noahknorr/mri-climate-chamber/3d-files/STLs/schlauchverbinderSchnellverschluss_verbinderHochflexibel-PVC_6.stl

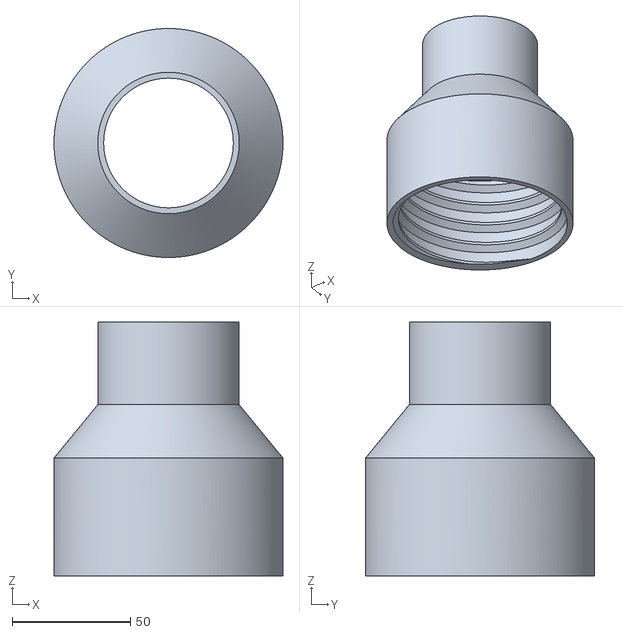
[picture p15: CAD file, 2026-01-19]
3d-files/STLs/schlauchverbinderSchnellverschluss_verbinderHochflexibel-PVC_6.stl
97.0 x 97.0 x 107.6
