noahknorr/mri-climate-chamber/3d-files/STLs/einsatz_SILKSCREEN_BOTTOM_36.stl

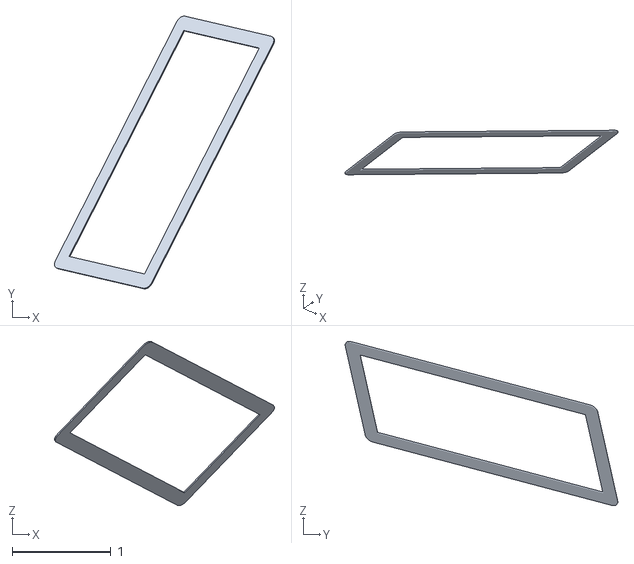
[picture p16: CAD file, 2026-01-19]
3d-files/STLs/einsatz_SILKSCREEN_BOTTOM_36.stl
2.23 x 2.77 x 1.67
