noahknorr/mri-climate-chamber/3d-files/STLs/schlauchverbinderSchnellverschluss_anschlussSuperflex_4.stl

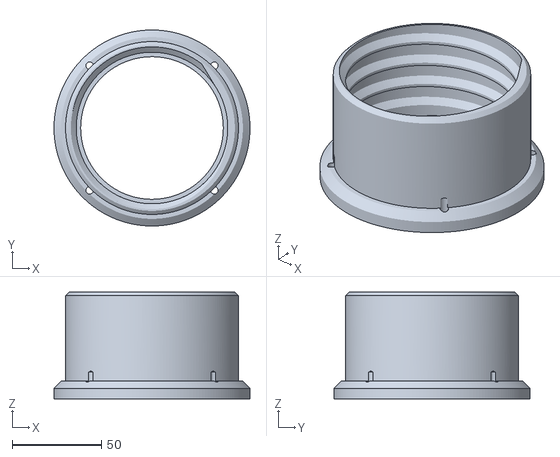
[picture p17: CAD file, 2026-01-19]
3d-files/STLs/schlauchverbinderSchnellverschluss_anschlussSuperflex_4.stl
110.0 x 110.0 x 60.0
