noahknorr/mri-climate-chamber/3d-files/STLs/einsatz_Dielectric_32.stl

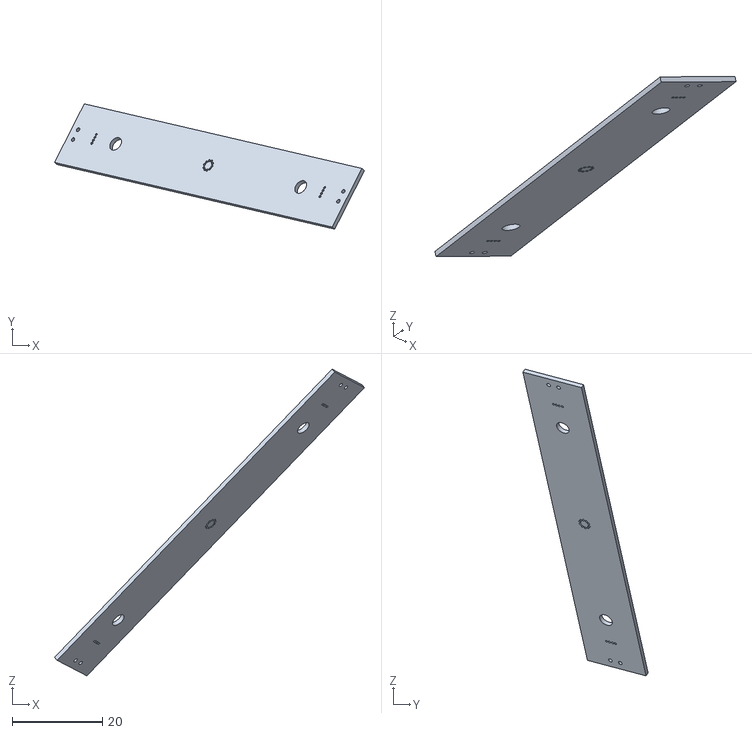
[picture p18: CAD file, 2026-01-19]
3d-files/STLs/einsatz_Dielectric_32.stl
68.8 x 27.8 x 68.1
