noahknorr/mri-climate-chamber/3d-files/STLs/einsatz_K1_18.stl

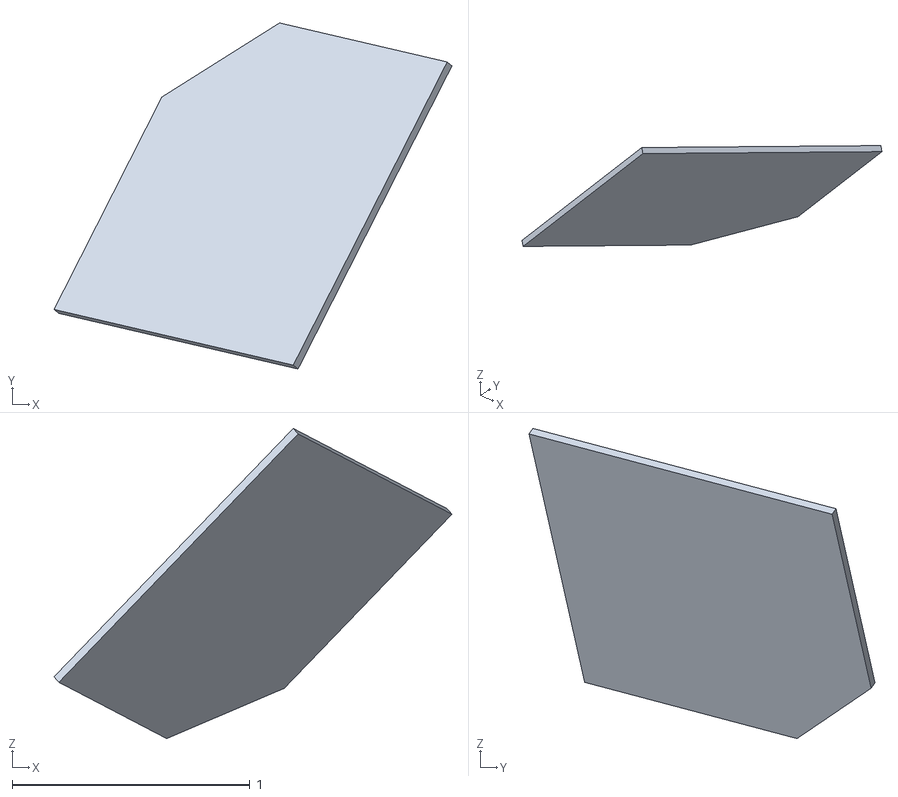
[picture p19: CAD file, 2026-01-19]
3d-files/STLs/einsatz_K1_18.stl
1.67 x 1.46 x 1.31
