noahknorr/mri-climate-chamber/3d-files/STLs/einsatz_bogenVerbinder_48.stl

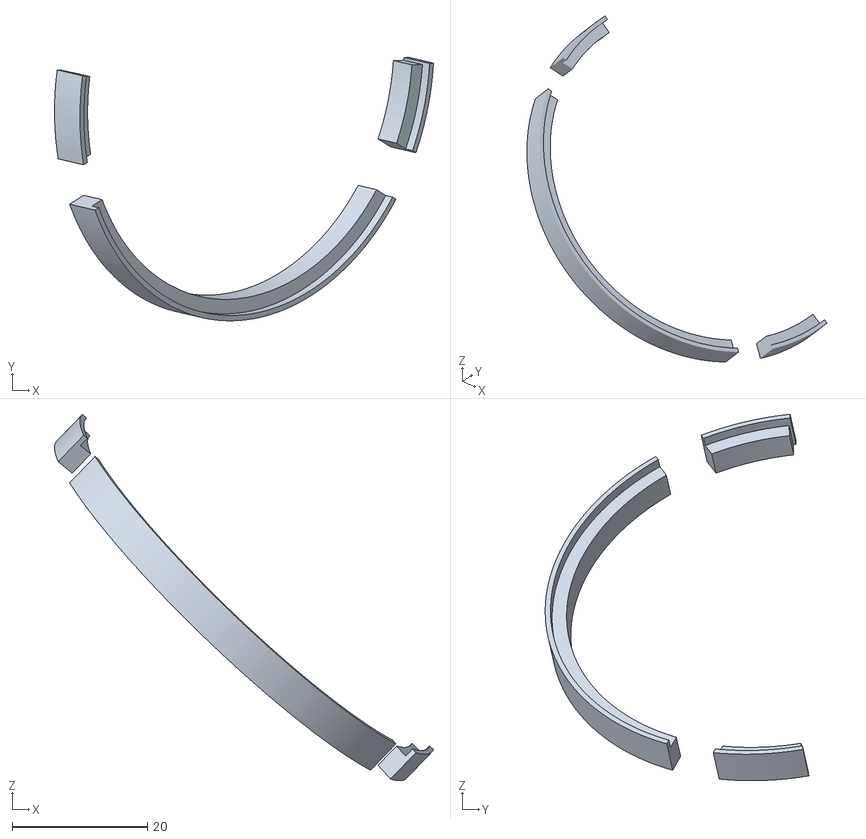
[picture p20: CAD file, 2026-01-19]
3d-files/STLs/einsatz_bogenVerbinder_48.stl
56.1 x 39.0 x 54.2
