noahknorr/mri-climate-chamber/3d-files/STLs/einsatz_HL2X_37.stl

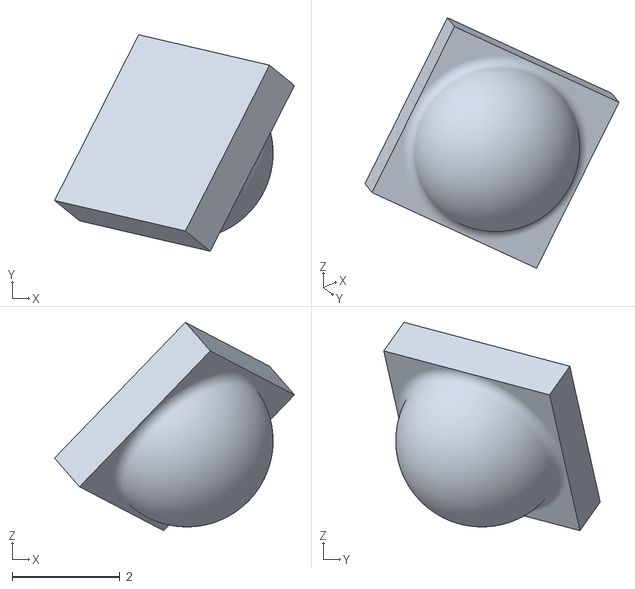
[picture p21: CAD file, 2026-01-19]
3d-files/STLs/einsatz_HL2X_37.stl
4.46 x 4.02 x 3.87
