noahknorr/mri-climate-chamber/3d-files/STLs/einsatz_TOP_31.stl

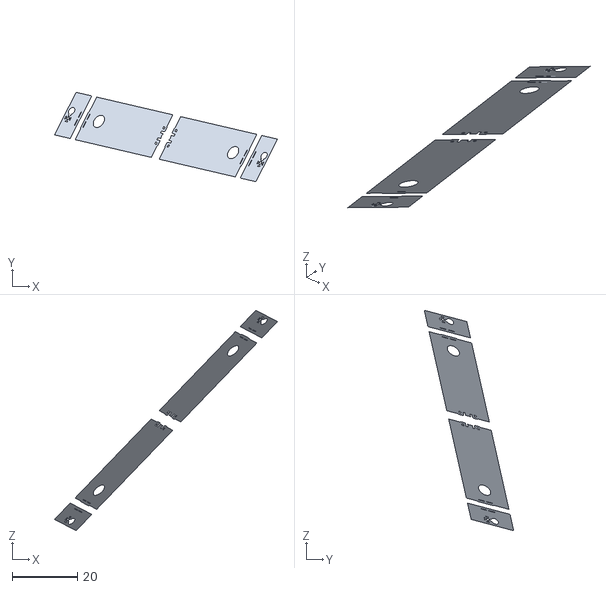
[picture p22: CAD file, 2026-01-19]
3d-files/STLs/einsatz_TOP_31.stl
68.3 x 27.4 x 67.5
