noahknorr/mri-climate-chamber/3d-files/STLs/einsatz_PIN_4_26.stl

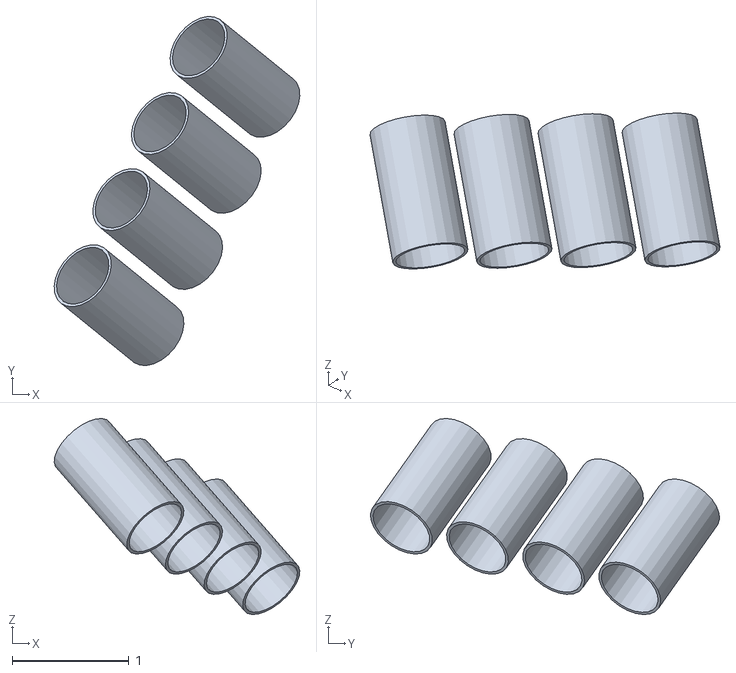
[picture p23: CAD file, 2026-01-19]
3d-files/STLs/einsatz_PIN_4_26.stl
2.10 x 2.98 x 1.68
