noahknorr/mri-climate-chamber/3d-files/STLs/einsatz_PASTEMASK_BOTTOM_35.stl

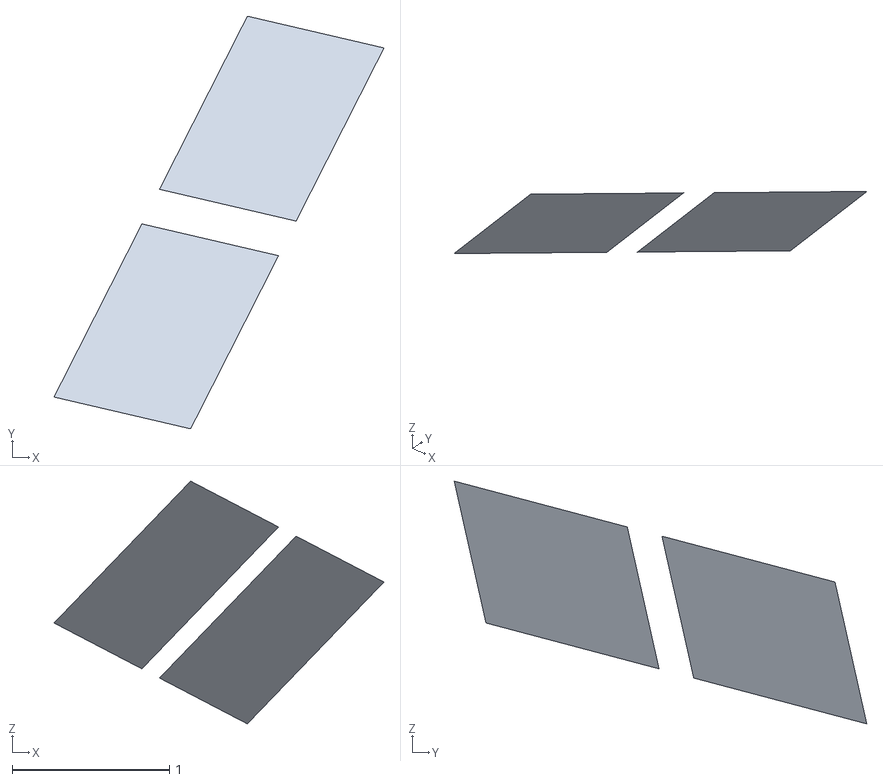
[picture p24: CAD file, 2026-01-19]
3d-files/STLs/einsatz_PASTEMASK_BOTTOM_35.stl
2.10 x 2.63 x 1.55
