noahknorr/mri-climate-chamber/3d-files/STLs/einsatz_1_2_4.stl

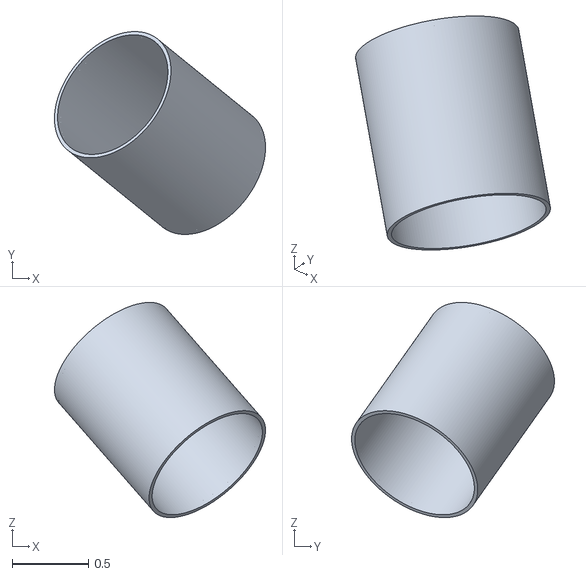
[picture p25: CAD file, 2026-01-19]
3d-files/STLs/einsatz_1_2_4.stl
1.39 x 1.33 x 1.41
