noahknorr/mri-climate-chamber/3d-files/STLs/einsatz_2_3_10.stl

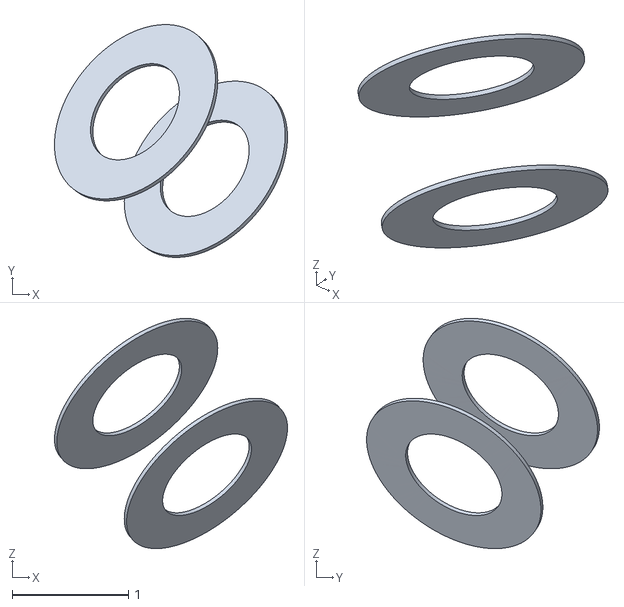
[picture p26: CAD file, 2026-01-19]
3d-files/STLs/einsatz_2_3_10.stl
2.01 x 2.01 x 1.98
