noahknorr/mri-climate-chamber/3d-files/STLs/einsatz_PFOSTEN_2P_41.stl

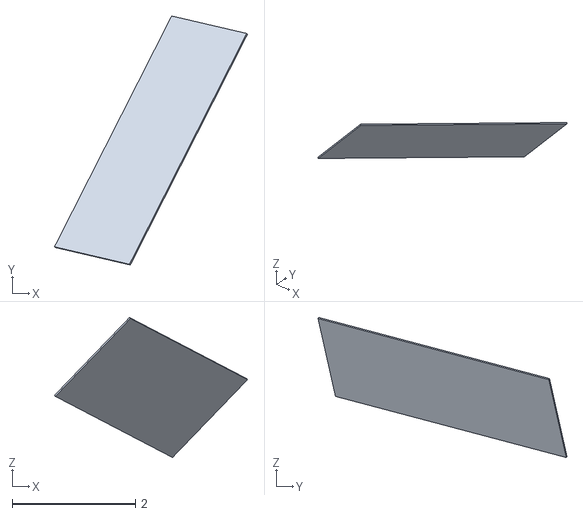
[picture p27: CAD file, 2026-01-19]
3d-files/STLs/einsatz_PFOSTEN_2P_41.stl
3.13 x 4.04 x 2.27
