noahknorr/mri-climate-chamber/3d-files/STLs/schlauchverbinderSchnellverschluss_grundeinsatz_1.stl

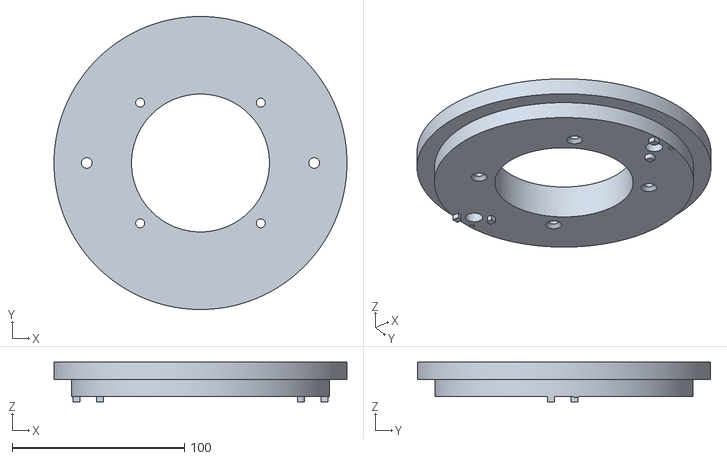
[picture p28: CAD file, 2026-01-19]
3d-files/STLs/schlauchverbinderSchnellverschluss_grundeinsatz_1.stl
170.0 x 170.0 x 23.0
