noahknorr/mri-climate-chamber/3d-files/STLs/schlauchverbinderSchnellverschluss_riegel_3.stl

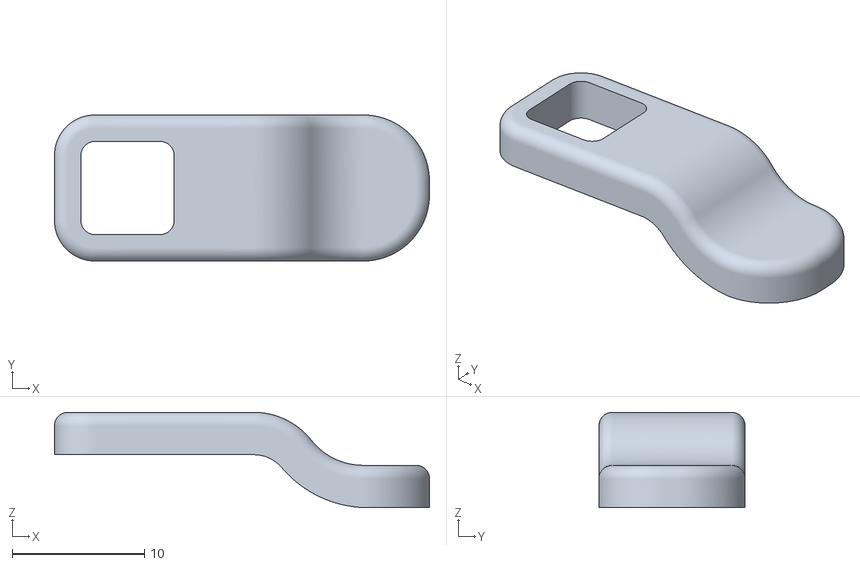
[picture p29: CAD file, 2026-01-19]
3d-files/STLs/schlauchverbinderSchnellverschluss_riegel_3.stl
28.3 x 11.0 x 7.20
