noahknorr/mri-climate-chamber/3d-files/STLs/schlauchverbinderSchnellverschluss_verbinderHebelRiegel_2.stl

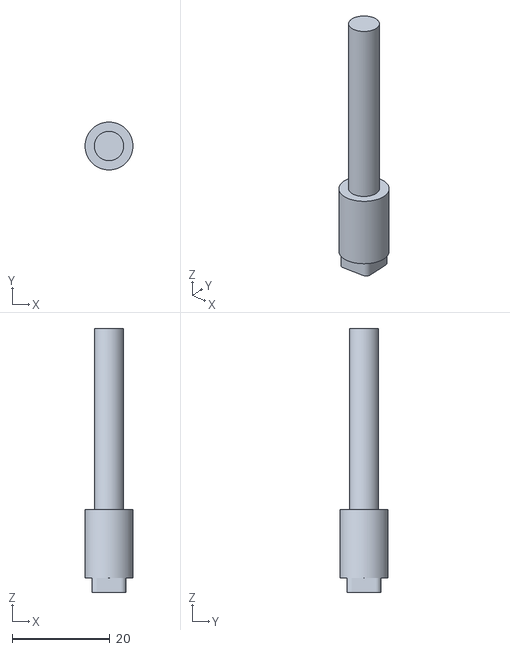
[picture p30: CAD file, 2026-01-19]
3d-files/STLs/schlauchverbinderSchnellverschluss_verbinderHebelRiegel_2.stl
9.80 x 9.79 x 54.0
