noahknorr/mri-climate-chamber/3d-files/STLs/einsatz_verbinderGrundrohrLaschen_47.stl

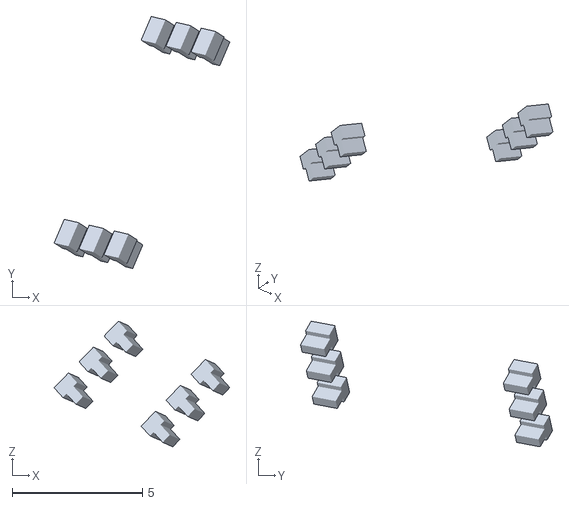
[picture p31: CAD file, 2026-01-19]
3d-files/STLs/einsatz_verbinderGrundrohrLaschen_47.stl
6.75 x 9.68 x 4.82
