noahknorr/mri-climate-chamber/3d-files/STLs/einsatz_aufsatzManschette_51.stl

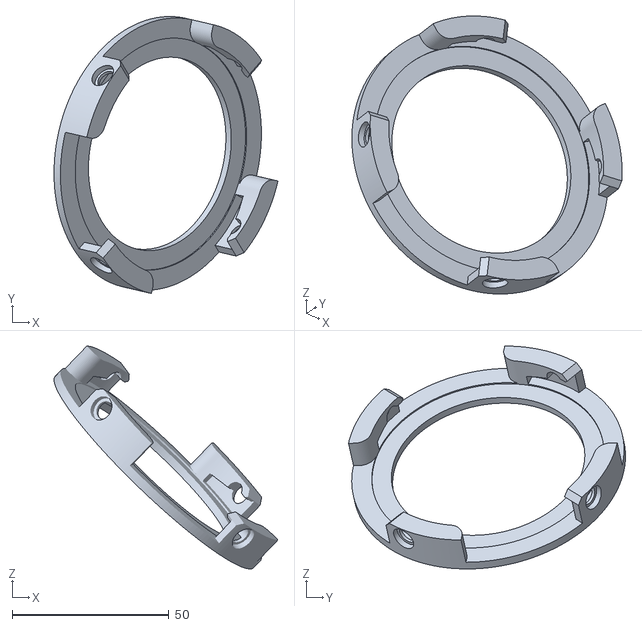
[picture p32: CAD file, 2026-01-19]
3d-files/STLs/einsatz_aufsatzManschette_51.stl
71.5 x 88.4 x 71.1
