noahknorr/mri-climate-chamber/3d-files/STLs/einsatz_verbinderPVC-Bajonett_54.stl

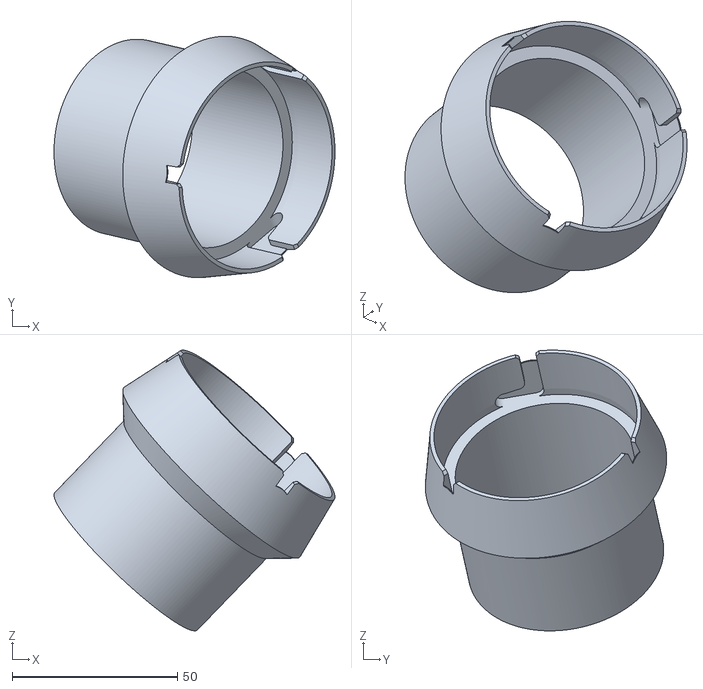
[picture p33: CAD file, 2026-01-19]
3d-files/STLs/einsatz_verbinderPVC-Bajonett_54.stl
85.0 x 73.0 x 84.9
