noahknorr/mri-climate-chamber/3d-files/STLs/einsatz_1_3_5.stl

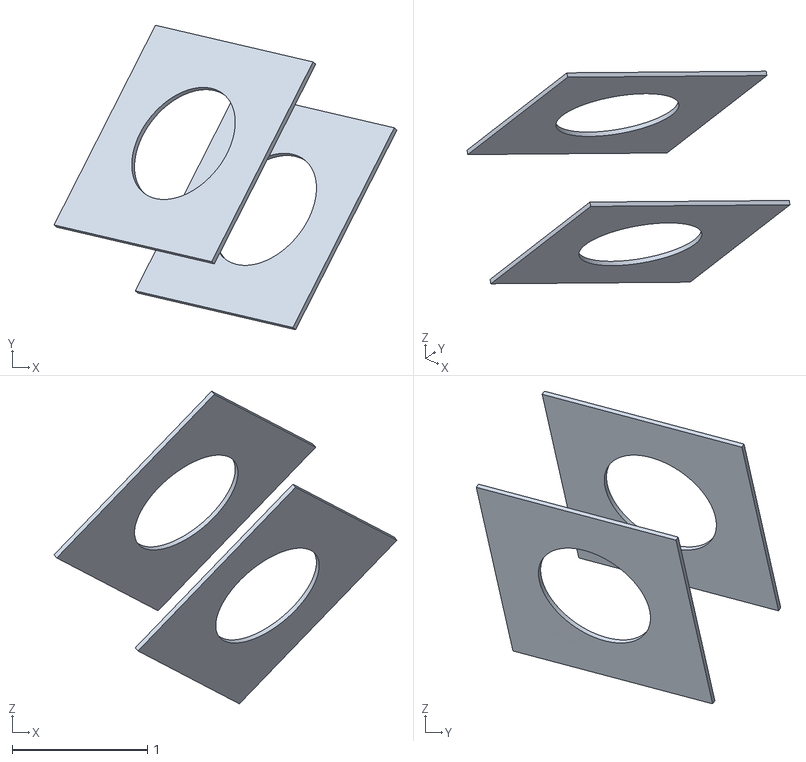
[picture p34: CAD file, 2026-01-19]
3d-files/STLs/einsatz_1_3_5.stl
2.54 x 2.25 x 2.31
