noahknorr/mri-climate-chamber/3d-files/STLs/einsatz_PIN_3_25.stl

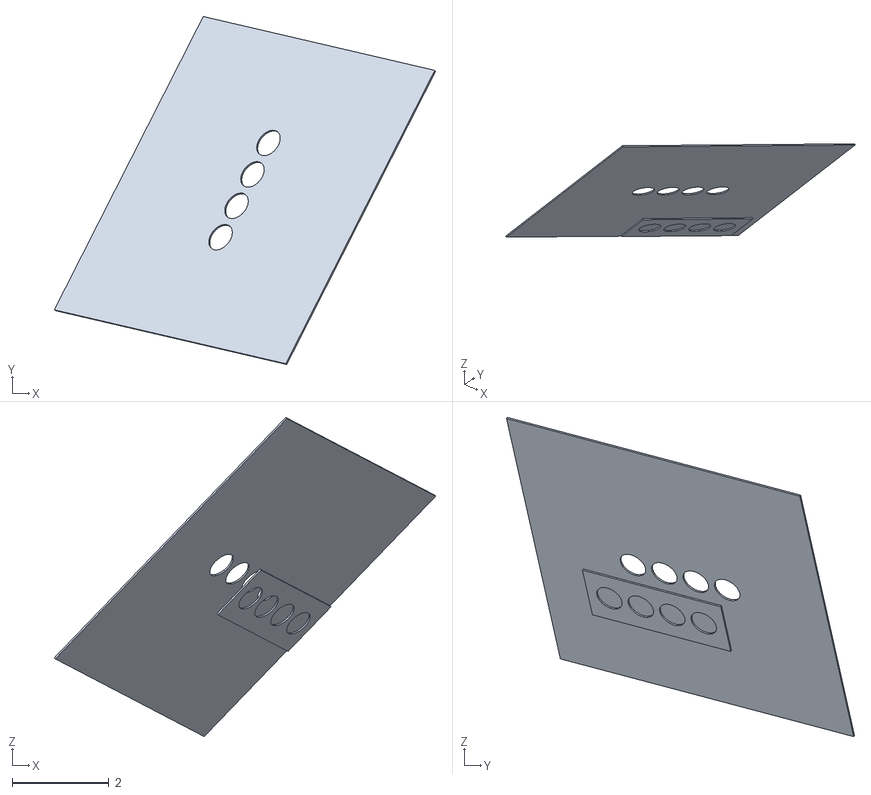
[picture p35: CAD file, 2026-01-19]
3d-files/STLs/einsatz_PIN_3_25.stl
7.90 x 7.21 x 6.61
