noahknorr/mri-climate-chamber/3d-files/STLs/einsatz_verbinderDeckelSeilichGummi2_59.stl

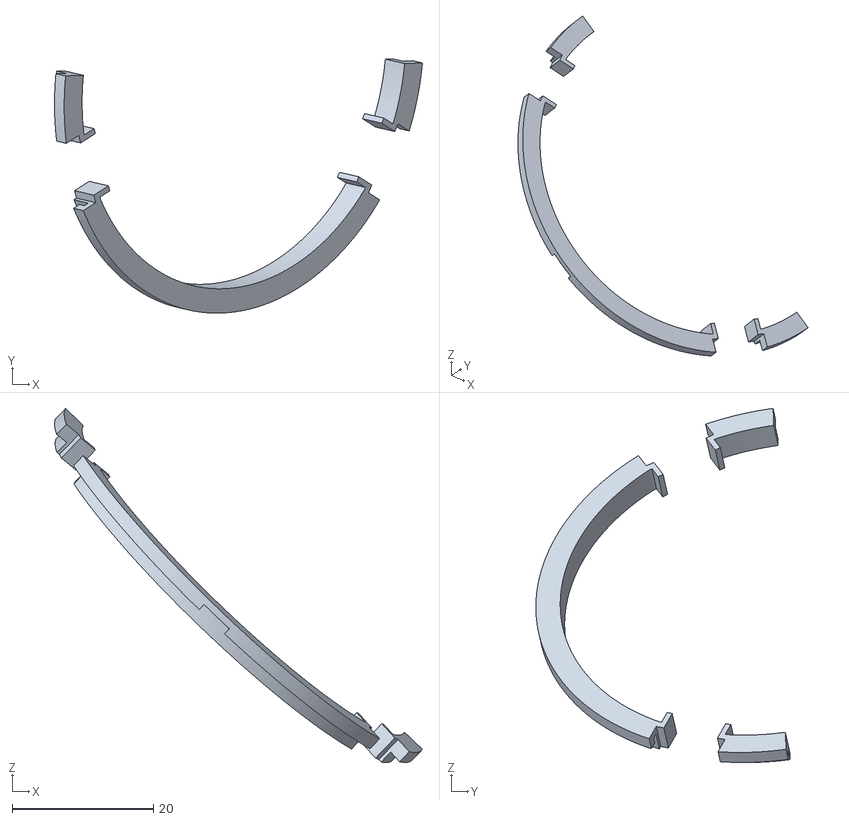
[picture p36: CAD file, 2026-01-19]
3d-files/STLs/einsatz_verbinderDeckelSeilichGummi2_59.stl
52.2 x 36.1 x 50.2
