noahknorr/mri-climate-chamber/3d-files/STLs/einsatz_A1_14.stl

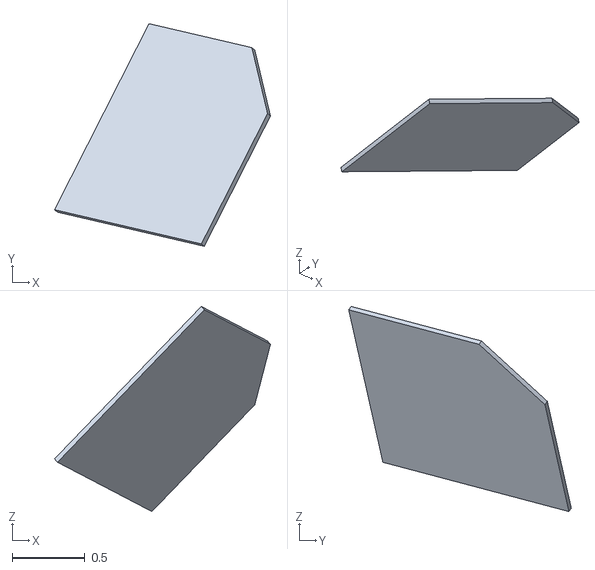
[picture p37: CAD file, 2026-01-19]
3d-files/STLs/einsatz_A1_14.stl
1.48 x 1.53 x 1.41
