noahknorr/mri-climate-chamber/3d-files/STLs/einsatz_SOLDERMASK_TOP_30.stl

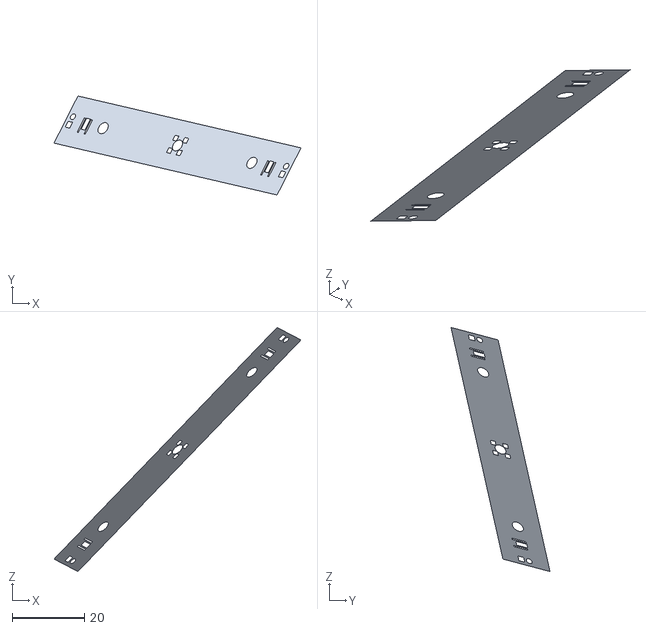
[picture p38: CAD file, 2026-01-19]
3d-files/STLs/einsatz_SOLDERMASK_TOP_30.stl
68.3 x 27.4 x 67.4
