noahknorr/mri-climate-chamber/3d-files/STLs/schlauchverbinderSchnellverschluss_flansch50mmLuefter_5.stl

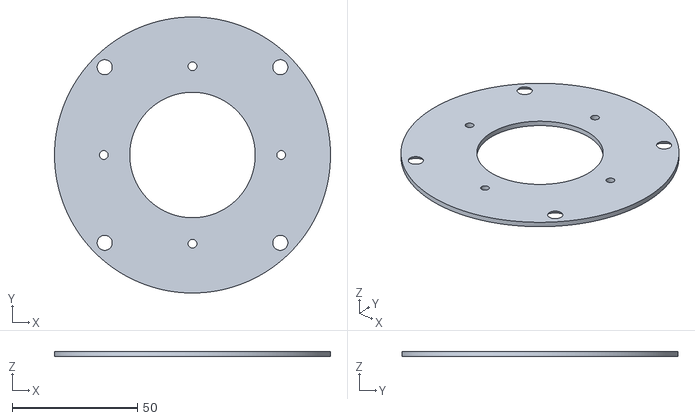
[picture p39: CAD file, 2026-01-19]
3d-files/STLs/schlauchverbinderSchnellverschluss_flansch50mmLuefter_5.stl
110.0 x 110.0 x 2.00
