noahknorr/mri-climate-chamber/3d-files/STLs/einsatz_SILKSCREEN_TOP_28.stl

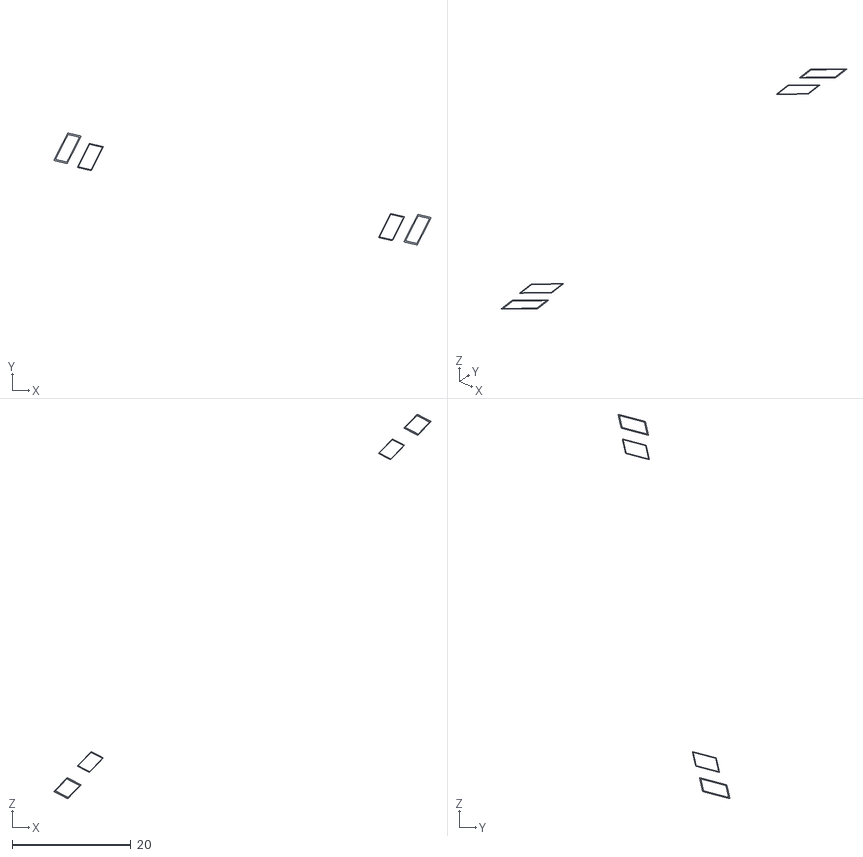
[picture p40: CAD file, 2026-01-19]
3d-files/STLs/einsatz_SILKSCREEN_TOP_28.stl
63.4 x 18.8 x 64.7
