noahknorr/mri-climate-chamber/3d-files/STLs/einsatz_aufsatzStatorStarr_53.stl

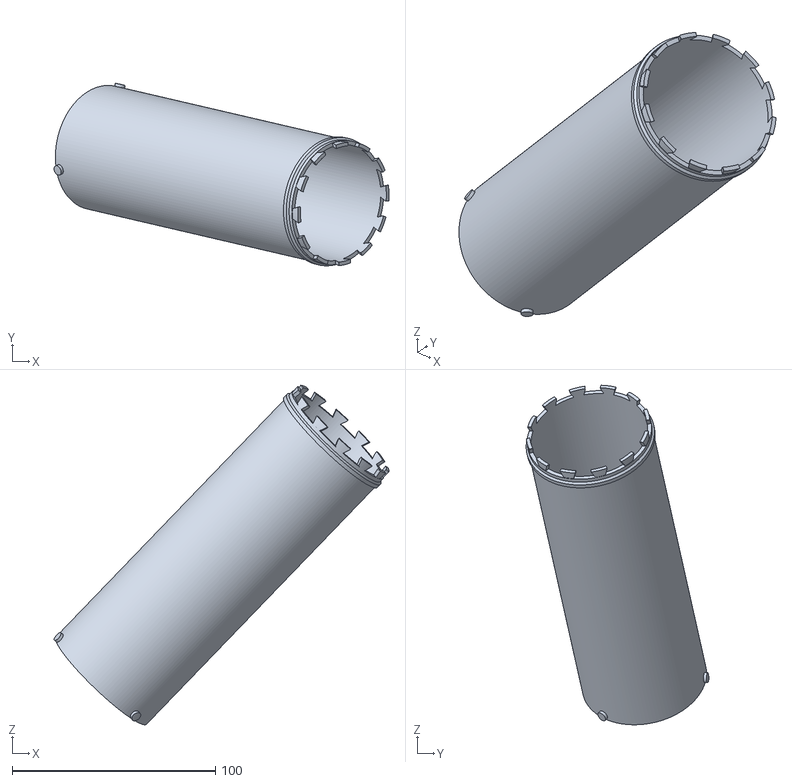
[picture p41: CAD file, 2026-01-19]
3d-files/STLs/einsatz_aufsatzStatorStarr_53.stl
164.9 x 89.9 x 167.1
