noahknorr/mri-climate-chamber/3d-files/STLs/einsatz_PIN_22.stl

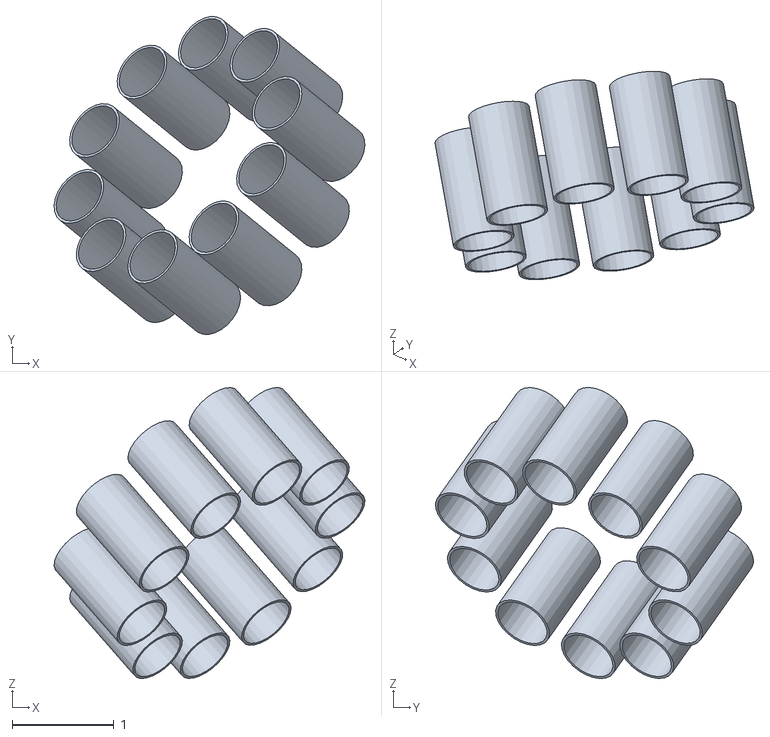
[picture p42: CAD file, 2026-01-19]
3d-files/STLs/einsatz_PIN_22.stl
3.06 x 3.13 x 2.87
