noahknorr/mri-climate-chamber/3d-files/STLs/einsatz_verbinderDeckelSeitlichEinsaetzeMitLaschen_58.stl

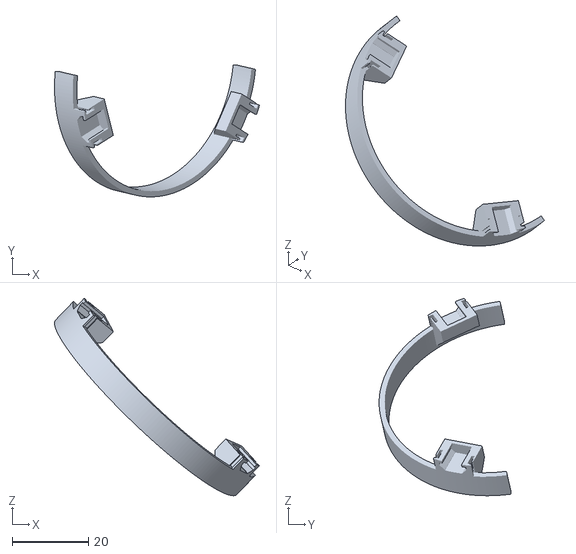
[picture p43: CAD file, 2026-01-19]
3d-files/STLs/einsatz_verbinderDeckelSeitlichEinsaetzeMitLaschen_58.stl
53.7 x 34.6 x 51.8
