noahknorr/mri-climate-chamber/3d-files/STLs/einsatz_LOTBRUCKE_2POL_39.stl

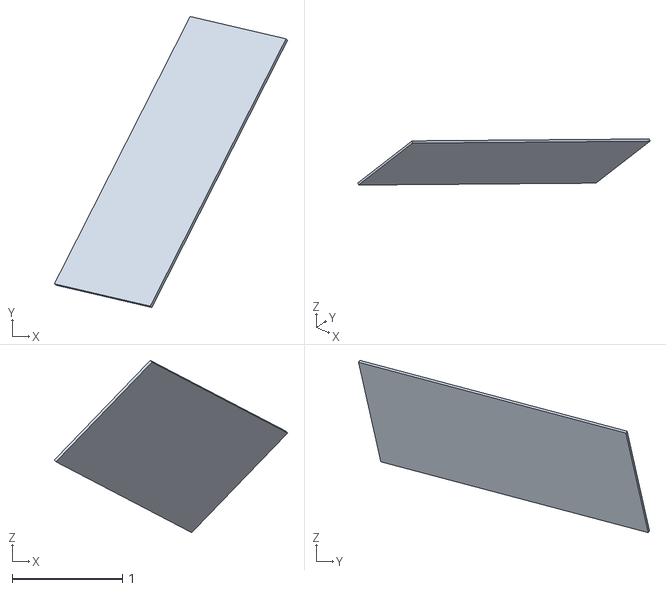
[picture p44: CAD file, 2026-01-19]
3d-files/STLs/einsatz_LOTBRUCKE_2POL_39.stl
2.12 x 2.64 x 1.56
