noahknorr/mri-climate-chamber/3d-files/STLs/einsatz_LZ1-00R202_40.stl

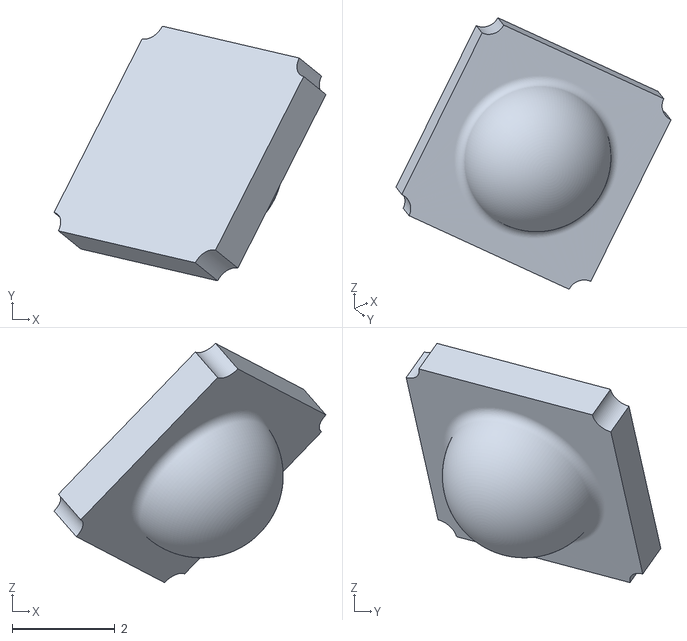
[picture p45: CAD file, 2026-01-19]
3d-files/STLs/einsatz_LZ1-00R202_40.stl
5.30 x 4.97 x 4.67
