noahknorr/mri-climate-chamber/3d-files/STLs/einsatz_deckelGegeneinsatz_57.stl

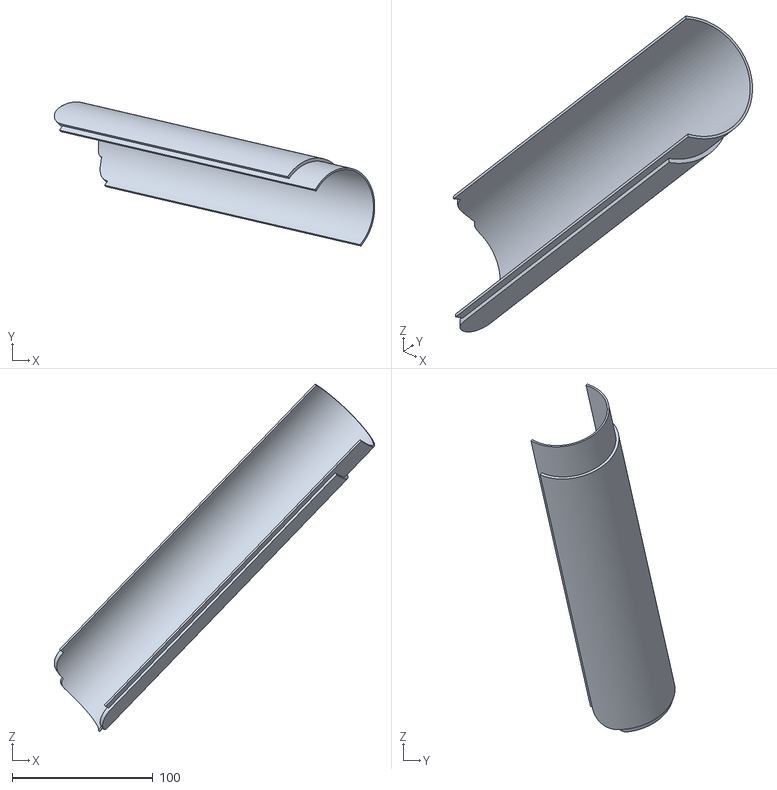
[picture p46: CAD file, 2026-01-19]
3d-files/STLs/einsatz_deckelGegeneinsatz_57.stl
227.5 x 102.3 x 247.1
