noahknorr/mri-climate-chamber/3d-files/STLs/einsatz_PASTEMASK_TOP_29.stl

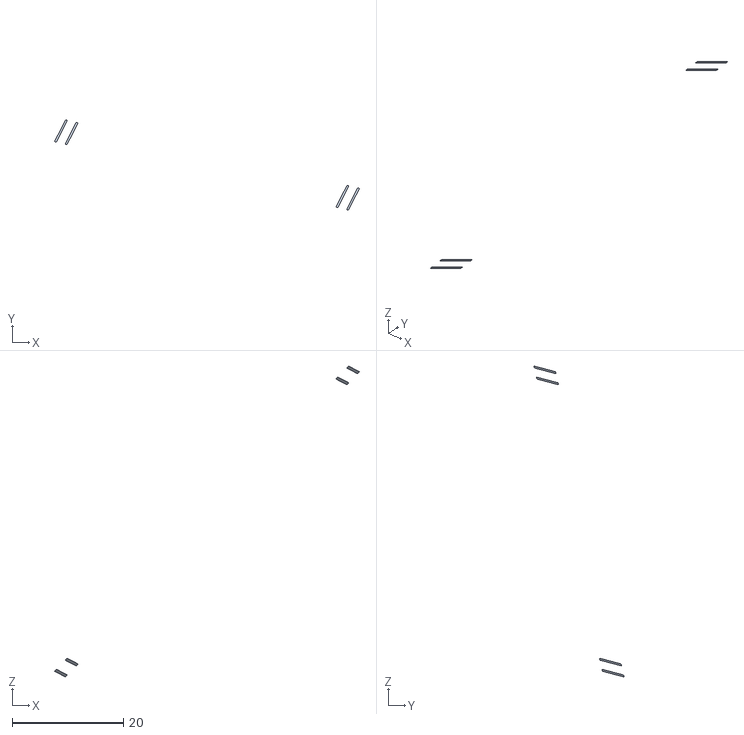
[picture p47: CAD file, 2026-01-19]
3d-files/STLs/einsatz_PASTEMASK_TOP_29.stl
54.9 x 16.2 x 56.0
